sercona/rc-elrs-live-channel-display/src/CrsfSerial.h

/*
   CrsfSerial.h
*/

#pragma once

#include <Arduino.h>

#include "crc8.h"
#include "crsf_protocol.h"


enum eFailsafeAction { fsaNoPulses, fsaHold };

class CrsfSerial
{
  public:
    // Packet timeout where buffer is flushed if no data is received in this time
    static const unsigned int CRSF_PACKET_TIMEOUT_MS = 100;
    static const unsigned int CRSF_FAILSAFE_STAGE1_MS = 300;

    CrsfSerial(HardwareSerial &port, uint32_t baud = CRSF_BAUDRATE);

    void begin(uint32_t baud = 0);

    void loop();

    void write(uint8_t b);
    void write(const uint8_t *buf, size_t len);

    void queuePacket(uint8_t addr, uint8_t type, const void *payload, uint8_t len);

    uint32_t getBaud() const {
      return _baud;
    };

    // Return current channel value (1-based) in us
    int getChannel(unsigned int ch) const {
      return _channels[ch - 1];
    }

    const crsfLinkStatistics_t *getLinkStatistics() const {
      return &_linkStatistics;
    }

    const crsf_sensor_gps_t *getGpsSensor() const {
      return &_gpsSensor;
    }

    bool isLinkUp() const {
      return _linkIsUp;
    }

    bool getPassthroughMode() const {
      return _passthroughBaud != 0;
    }

    void setPassthroughMode(bool val, uint32_t passthroughBaud = 0);

    // Event Handlers
    void (*onLinkUp)();
    void (*onLinkDown)();

    // OobData is any byte which is not CRSF, including passthrough
    void (*onOobData)(uint8_t b);

    // CRSF Packet Callbacks
    void (*onPacketChannels)();
    void (*onPacketLinkStatistics)(crsfLinkStatistics_t *ls);
    void (*onPacketGps)(crsf_sensor_gps_t *gpsSensor);

  private:
    HardwareSerial &_port;
    uint8_t _rxBuf[CRSF_MAX_PACKET_SIZE];
    uint8_t _rxBufPos;
    Crc8 _crc;
    crsfLinkStatistics_t _linkStatistics;
    crsf_sensor_gps_t _gpsSensor;
    uint32_t _baud;
    uint32_t _lastReceive;
    uint32_t _lastChannelsPacket;
    bool _linkIsUp;
    uint32_t _passthroughBaud;
    int _channels[CRSF_NUM_CHANNELS];

    void handleSerialIn();
    void handleByteReceived();
    void shiftRxBuffer(uint8_t cnt);
    void processPacketIn(uint8_t len);
    void checkPacketTimeout();
    void checkLinkDown();

    // Packet Handlers
    void packetChannelsPacked(const crsf_header_t *p);
    void packetLinkStatistics(const crsf_header_t *p);
    void packetGps(const crsf_header_t *p);
};
