sercona/rc-elrs-live-channel-display/src/crc8.h

/*
 * crc8.h
 */

#pragma once

#include <stdint.h>

class Crc8
{
  public:
    Crc8(uint8_t poly);
    uint8_t calc(uint8_t *data, uint8_t len);

  protected:
    uint8_t _lut[256];
    void init(uint8_t poly);
};
